aprochazka/ProfilometerProbe/Firmware/Core/Cam/OV5642_regs.h

/**
 ******************************************************************************
 * @file           : OV5642_regs.h
 * @brief          : Predefined registers configurations for camera chip. 
 *                   This file contains settings for registers to achieve specific camera chip configuration.
 * 					 This file was taken over from ArduCam repository and edited to work for this specific project. 
 * @author         : Adam Prochazka <xproch0f>
 ******************************************************************************
 */

#include "stdint.h"
#include "stdlib.h"
#include "stdio.h"
#include "string.h"

typedef struct sensor_reg
{
	uint16_t reg;
	uint8_t val;
} sensor_reg;

static const struct sensor_reg ov5642_320x240[]  =
{
	{0x3800 ,0x1 },
	{0x3801 ,0xa8},
	{0x3802 ,0x0 },
	{0x3803 ,0xA },
	{0x3804 ,0xA },
	{0x3805 ,0x20},
	{0x3806 ,0x7 },
	{0x3807 ,0x98},
	{0x3808 ,0x1 },
	{0x3809 ,0x40},
	{0x380a ,0x0 },
	{0x380b ,0xF0},
	{0x380c ,0xc },
	{0x380d ,0x80},
	{0x380e ,0x7 },
	{0x380f ,0xd0},
	{0x5001 ,0x7f},
	{0x5680 ,0x0 },
	{0x5681 ,0x0 },
	{0x5682 ,0xA },
	{0x5683 ,0x20},
	{0x5684 ,0x0 },
	{0x5685 ,0x0 },
	{0x5686 ,0x7 },
	{0x5687 ,0x98},
	{0x3801, 0xb0},
	{0xffff, 0xff},
};

static const struct sensor_reg ov5642_1024x768[] =
	{
		{0x3800, 0x1},
		{0x3801, 0xB0},
		{0x3802, 0x0},
		{0x3803, 0xA},
		{0x3804, 0xA},
		{0x3805, 0x20},
		{0x3806, 0x7},
		{0x3807, 0x98},
		{0x3808, 0x4},
		{0x3809, 0x0},
		{0x380a, 0x3},
		{0x380b, 0x0},
		{0x380c, 0xc},
		{0x380d, 0x80},
		{0x380e, 0x7},
		{0x380f, 0xd0},
		{0x5001, 0x7f},
		{0x5680, 0x0},
		{0x5681, 0x0},
		{0x5682, 0xA},
		{0x5683, 0x20},
		{0x5684, 0x0},
		{0x5685, 0x0},
		{0x5686, 0x7},
		{0x5687, 0x98},
		{0xffff, 0xff},
};

static const struct sensor_reg OV5642_QVGA_Preview[]  =
{
	{0x3103 ,0x93},
	{0x3008 ,0x82},
	{0x3017 ,0x7f},
	{0x3018 ,0xfc},
	{0x3810 ,0xc2},
	{0x3615 ,0xf0},
	{0x3000 ,0x00},
	{0x3001 ,0x00},
	{0x3002 ,0x5c},
	{0x3003 ,0x00},
	{0x3004 ,0xff},
	{0x3005 ,0xff},
	{0x3006 ,0x43},
	{0x3007 ,0x37},
	{0x3011 ,0x08},
	{0x3010 ,0x10},
	{0x460c ,0x22},
	{0x3815 ,0x04},
	{0x370c ,0xa0},
	{0x3602 ,0xfc},
	{0x3612 ,0xff},
	{0x3634 ,0xc0},
	{0x3613 ,0x00},
	{0x3605 ,0x7c},
	{0x3621 ,0x09},
	{0x3622 ,0x60},
	{0x3604 ,0x40},
	{0x3603 ,0xa7},
	{0x3603 ,0x27},
	{0x4000 ,0x21},
	{0x401d ,0x22},
	{0x3600 ,0x54},
	{0x3605 ,0x04},
	{0x3606 ,0x3f},
	{0x3c01 ,0x80},
	{0x5000 ,0x4f},
	{0x5020 ,0x04},
	{0x5181 ,0x79},
	{0x5182 ,0x00},
	{0x5185 ,0x22},
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
	         
	{0x5800 ,0x48},
	{0x5801 ,0x31},
	{0x5802 ,0x21},
	{0x5803 ,0x1b},
	{0x5804 ,0x1a},
	{0x5805 ,0x1e},
	{0x5806 ,0x29},
	{0x5807 ,0x38},
	{0x5808 ,0x26},
	{0x5809 ,0x17},
	{0x580a ,0x11},
	{0x580b ,0x0e },
	{0x580c ,0x0d },
	{0x580d ,0x0e },
	{0x580e ,0x13},
	{0x580f ,0x1a},
	{0x5810 ,0x15},
	{0x5811 ,0x0d },
	{0x5812 ,0x08 },
	{0x5813 ,0x05 },
	{0x5814 ,0x04 },
	{0x5815 ,0x05 },
	{0x5816 ,0x09 },
	{0x5817 ,0x0d },
	{0x5818 ,0x11},
	{0x5819 ,0x0a },
	{0x581a ,0x04 },
	{0x581b ,0x00 },
	{0x581c ,0x00 },
	{0x581d ,0x01 },
	{0x581e ,0x06 },
	{0x581f ,0x09 },
	{0x5820 ,0x12},
	{0x5821 ,0x0b },
	{0x5822 ,0x04 },
	{0x5823 ,0x00 },
	{0x5824 ,0x00 },
	{0x5825 ,0x01 },
	{0x5826 ,0x06 },
	{0x5827 ,0x0a },
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
	        
	{0x5180 ,0xff},
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
	{0x3a00 ,0x78},	//AEC System Control 0
	{0x3a0d ,0x10},	//60 Hz Max Bands in One Frame
	{0x3a0e ,0x0d},	//50 Hz Max Bands in One Frame
	{0x3a10 ,0x32},	//Stable Range Low Limit (enter)
	{0x3a1b ,0x3c},	//Stable Range High Limit (go out)
	{0x3a1e ,0x32},	//Stable Range Low Limit (go out)
	{0x3a11 ,0x80},	//Step Manual Mode, Fast Zone High Limit
	{0x3a1f ,0x20},	//Step Manual Mode, Fast Zone Low Limit
	{0x3a00 ,0x78},	//AEC System Control 0
	{0x460b ,0x35},	//RSV VFIFO Control 0B
	{0x471d ,0x00},	//DVP CONTROL 1D
	{0x4713 ,0x03},	//COMPRESSION MODE SELECT mode3
	{0x471c ,0x50},	//RSV
	{0x5682 ,0x0a},	//AVG X END
	{0x5683 ,0x20},	//AVG X END
	{0x5686 ,0x07},	//AVG Y END
	{0x5687 ,0x98},	//AVG Y END
	{0x5001 ,0x4f},	//ISP CONTROL 01, UV adjust/Line stretch/UV average/Color matrix/AWB enable
	{0x589b ,0x00}, //RSV
	{0x589a ,0xc0},	//RSV
	{0x4407 ,0x08},	//COMPRESSION CTRL07 Bit[5:0]: Quantization scale  0x02
	{0x589b ,0x00},	//RSV
	{0x589a ,0xc0},	//RSV
	{0x3002 ,0x0c},	//Reset for Individual Block, Reset SFIFO/compression
	{0x3002 ,0x00},	//Reset for Individual Block
	{0x3503 ,0x00},	//AEC Manual Mode Control, Auto enable
	//{0x3818, 0xa8},
	//{0x3621, 0x17},
	//{0x3801, 0xb0},
	{0x5025, 0x80},
	{0x3a0f, 0x48},
	{0x3a10, 0x40},
	{0x3a1b, 0x4a},
	{0x3a1e, 0x3e},
	{0x3a11, 0x70},
	{0x3a1f, 0x20},
	{0xffff, 0xff},
};
